maxaudron/woodox/hardware/kicad_lib/marbastlib/3d/CON_MJ-4PP-9.step

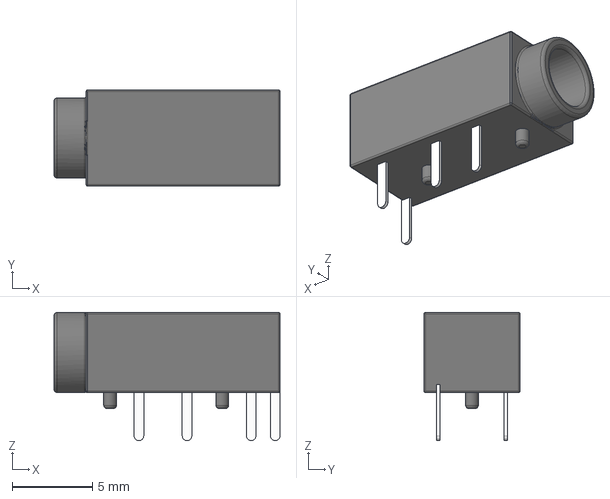
[picture p17: CAD file, 2026-05-16]
hardware/kicad_lib/marbastlib/3d/CON_MJ-4PP-9.step
14.1 x 6.00 x 8.00 mm
