maxaudron/woodox/hardware/kicad_lib/marbastlib/3d/HS_Kailh_MX.step

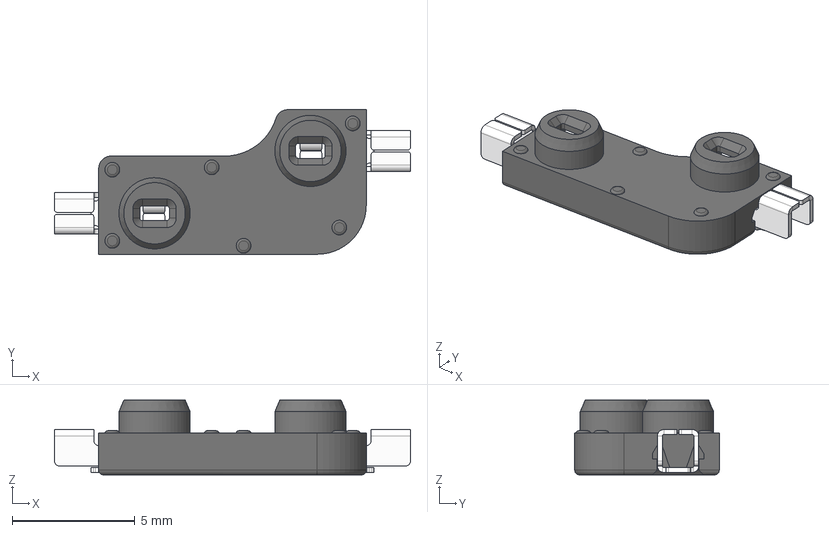
[picture p18: CAD file, 2026-05-16]
hardware/kicad_lib/marbastlib/3d/HS_Kailh_MX.step
14.5 x 5.89 x 3.05 mm
Contact x 2
