maxaudron/woodox/hardware/kicad_lib/marbastlib/3d/PNT_RKJXU1210006.step

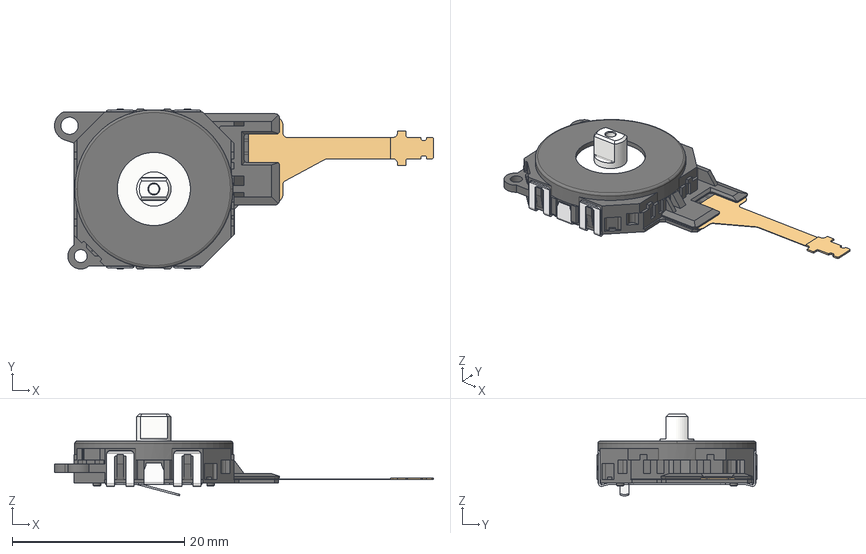
[picture p20: CAD file, 2026-05-16]
hardware/kicad_lib/marbastlib/3d/PNT_RKJXU1210006.step
44.0 x 18.6 x 9.50 mm
