maxaudron/woodox/hardware/kicad_lib/marbastlib/3d/SW_SSSS223900.step

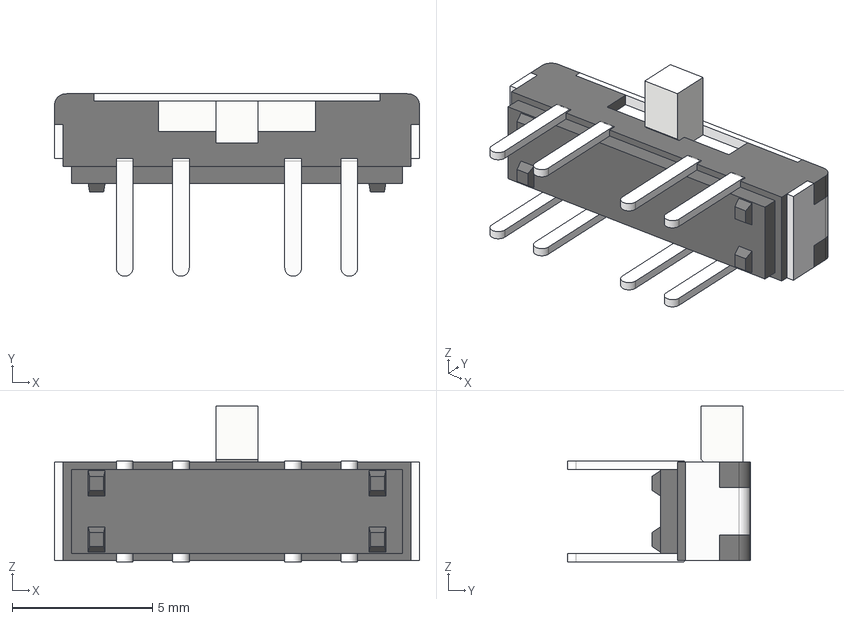
[picture p21: CAD file, 2026-05-16]
hardware/kicad_lib/marbastlib/3d/SW_SSSS223900.step
13.0 x 6.50 x 5.55 mm
