maxaudron/woodox/hardware/kicad_lib/marbastlib/3d/MSK12C02.step

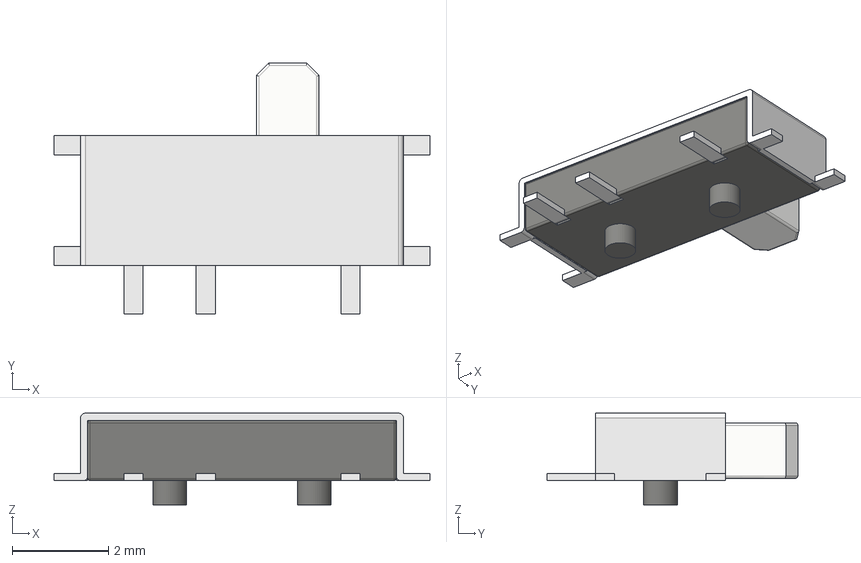
[picture p22: CAD file, 2026-05-16]
hardware/kicad_lib/marbastlib/3d/MSK12C02.step
7.80 x 5.20 x 1.90 mm
