maxaudron/woodox/hardware/kicad_lib/marbastlib/3d/ROT_EC11N.step

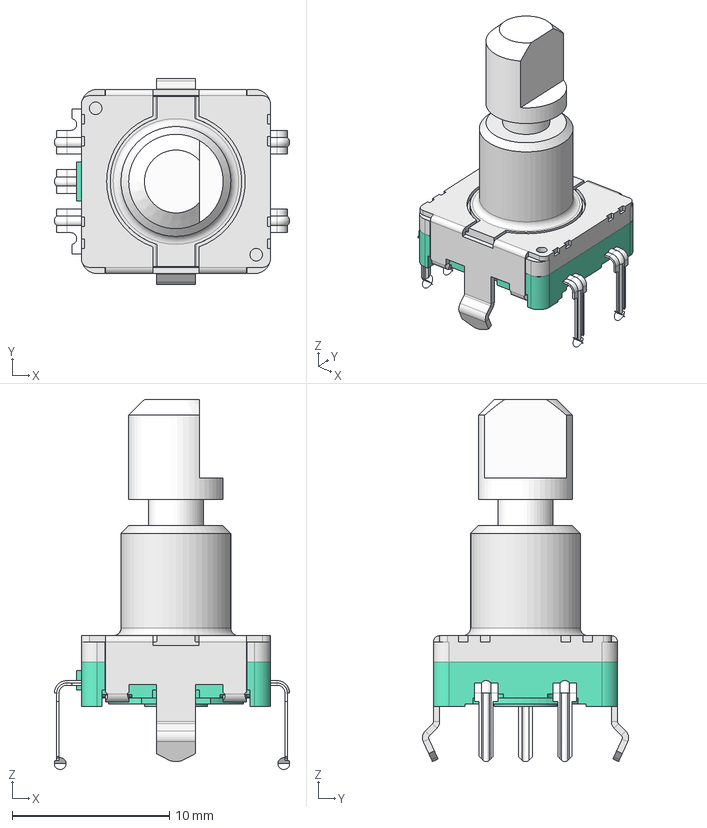
[picture p23: CAD file, 2026-05-16]
hardware/kicad_lib/marbastlib/3d/ROT_EC11N.step
14.9 x 13.1 x 23.5 mm
