maxaudron/woodox/hardware/kicad_lib/marbastlib/3d/HS_Kailh_Choc.step

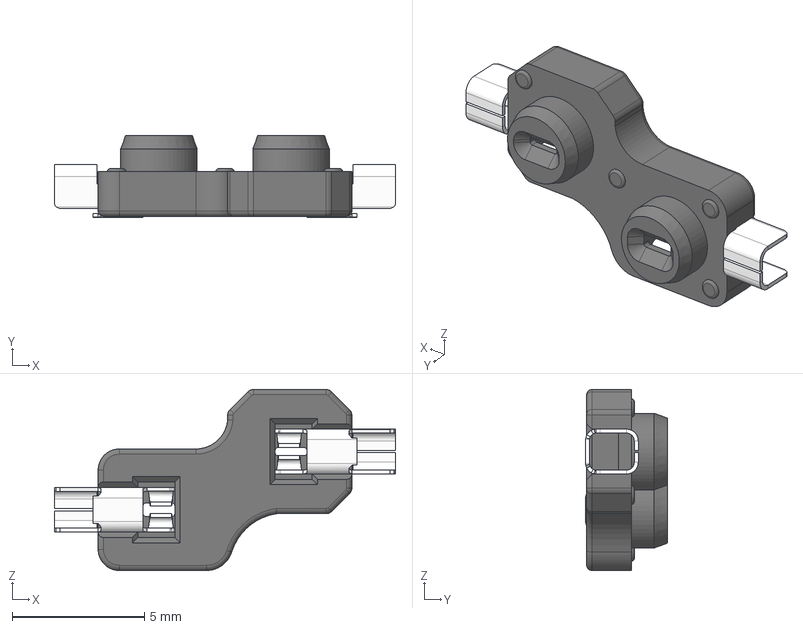
[picture p24: CAD file, 2026-05-16]
hardware/kicad_lib/marbastlib/3d/HS_Kailh_Choc.step
12.9 x 3.09 x 6.85 mm
pin x 2
socket
