maxaudron/woodox/hardware/kicad_lib/marbastlib/3d/CON_SM07B-SRSS-TB.step

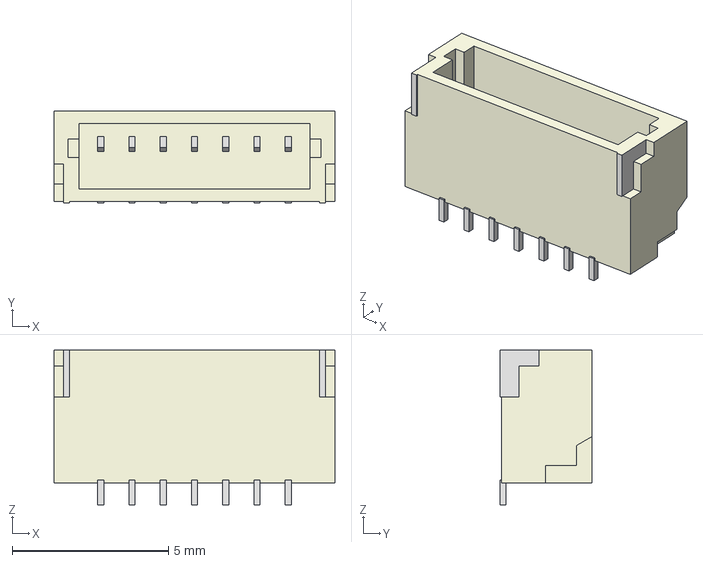
[picture p25: CAD file, 2026-05-16]
hardware/kicad_lib/marbastlib/3d/CON_SM07B-SRSS-TB.step
9.00 x 2.96 x 4.95 mm
