maxaudron/woodox/hardware/kicad_lib/marbastlib/3d/ROT_EC11E.step

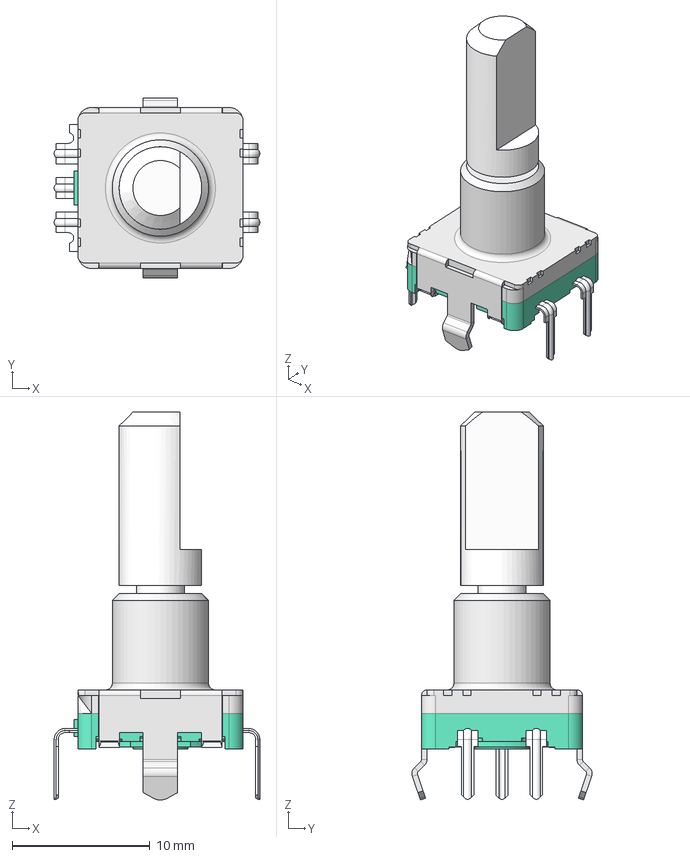
[picture p26: CAD file, 2026-05-16]
hardware/kicad_lib/marbastlib/3d/ROT_EC11E.step
14.9 x 13.1 x 28.2 mm
