maxaudron/woodox/hardware/kicad_lib/marbastlib/3d/SW_SKHLLC.step

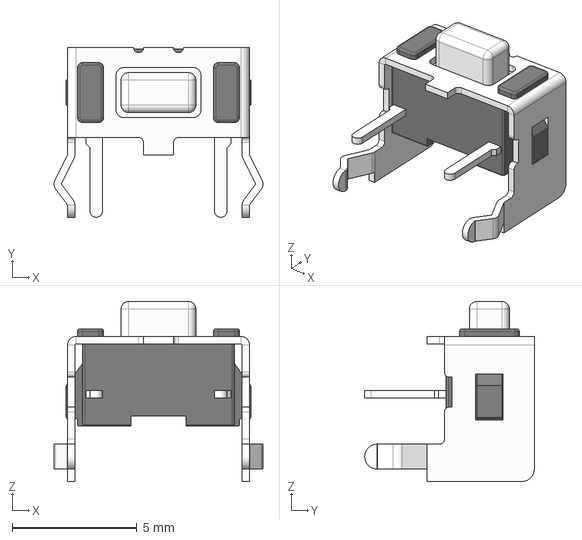
[picture p27: CAD file, 2026-05-16]
hardware/kicad_lib/marbastlib/3d/SW_SKHLLC.step
8.38 x 6.80 x 7.22 mm
