maxaudron/woodox/hardware/kicad_lib/marbastlib/3d/Crystal_FA-128.step

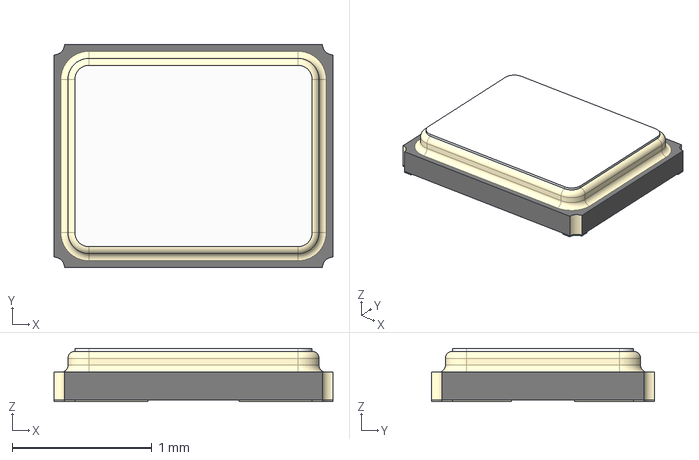
[picture p28: CAD file, 2026-05-16]
hardware/kicad_lib/marbastlib/3d/Crystal_FA-128.step
2.00 x 1.60 x 0.38 mm
