maxaudron/woodox/hardware/kicad_lib/marbastlib/3d/LED_SK6812MINI-E.step

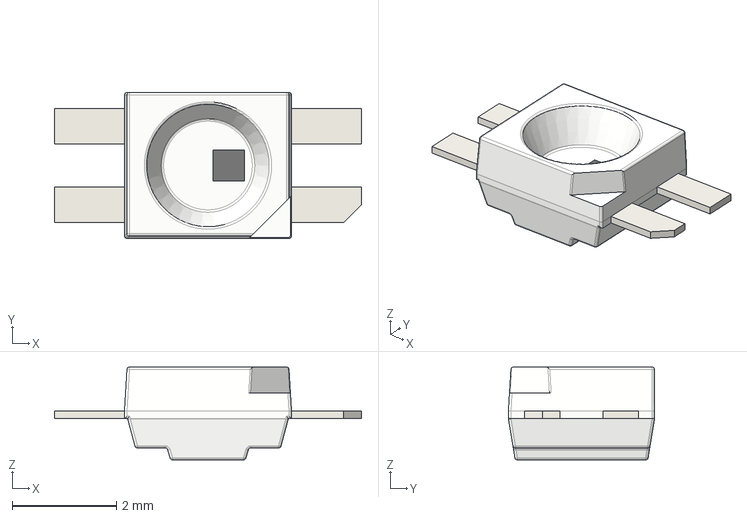
[picture p29: CAD file, 2026-05-16]
hardware/kicad_lib/marbastlib/3d/LED_SK6812MINI-E.step
5.88 x 2.80 x 1.78 mm
