maxaudron/woodox/hardware/kicad_lib/marbastlib/3d/holyiot_18010_nRF52840.step

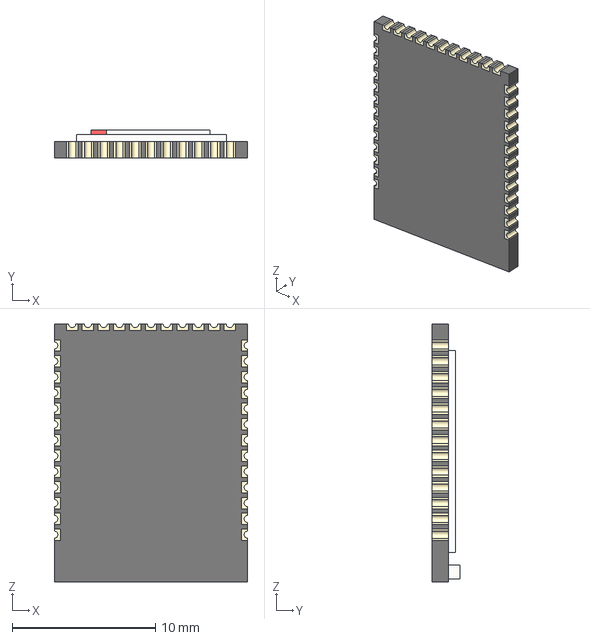
[picture p30: CAD file, 2026-05-16]
hardware/kicad_lib/marbastlib/3d/holyiot_18010_nRF52840.step
13.5 x 1.92 x 18.0 mm
