maxaudron/woodox/hardware/kicad_lib/marbastlib/3d/CON_BM02B-ACHSS.step

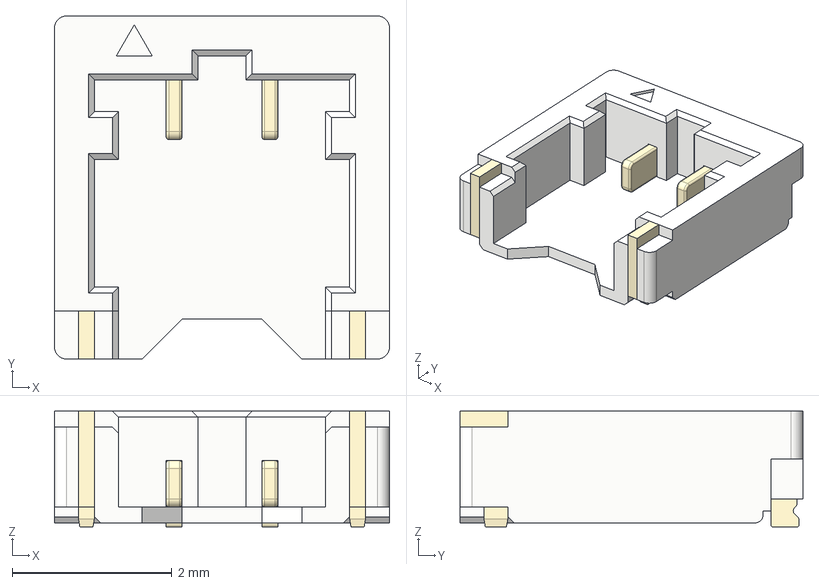
[picture p31: CAD file, 2026-05-16]
hardware/kicad_lib/marbastlib/3d/CON_BM02B-ACHSS.step
4.20 x 4.30 x 1.45 mm
