maxaudron/woodox/hardware/kicad_lib/marbastlib/3d/moko_mk08a_nRF52840.step

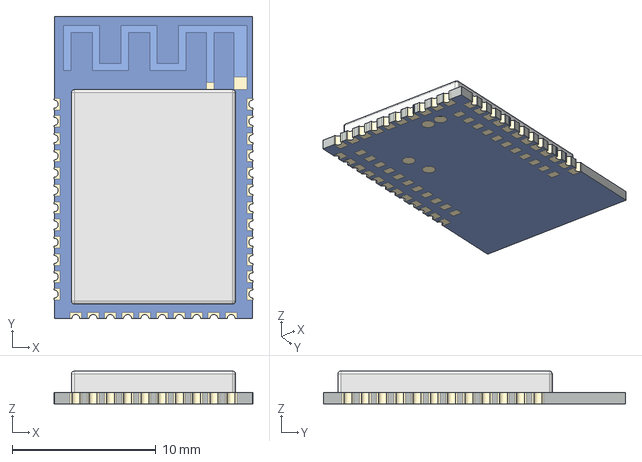
[picture p32: CAD file, 2026-05-16]
hardware/kicad_lib/marbastlib/3d/moko_mk08a_nRF52840.step
13.8 x 21.0 x 2.29 mm
