maxaudron/woodox/hardware/kicad_lib/marbastlib/3d/CON_SM08B-SRSS-TB.step

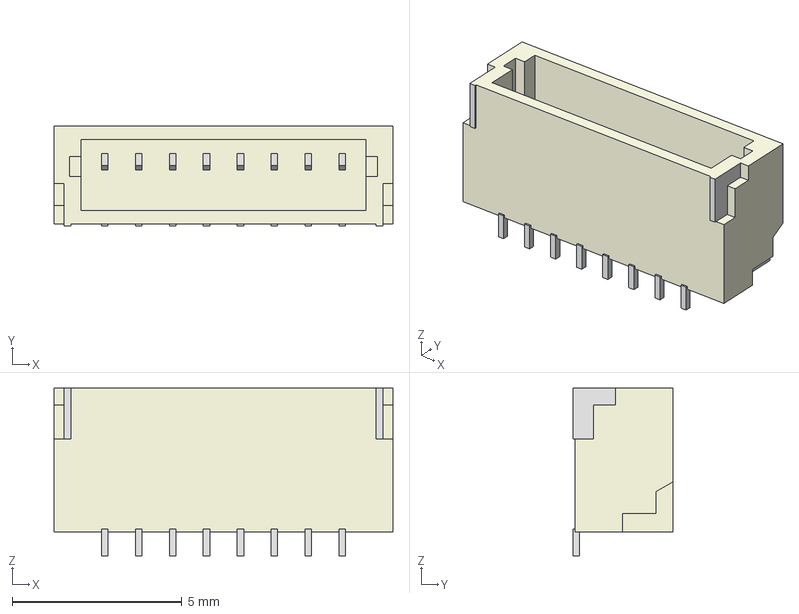
[picture p33: CAD file, 2026-05-16]
hardware/kicad_lib/marbastlib/3d/CON_SM08B-SRSS-TB.step
10.0 x 2.96 x 4.95 mm
