maxaudron/woodox/hardware/kicad_lib/marbastlib/3d/SW_ESP3020.step

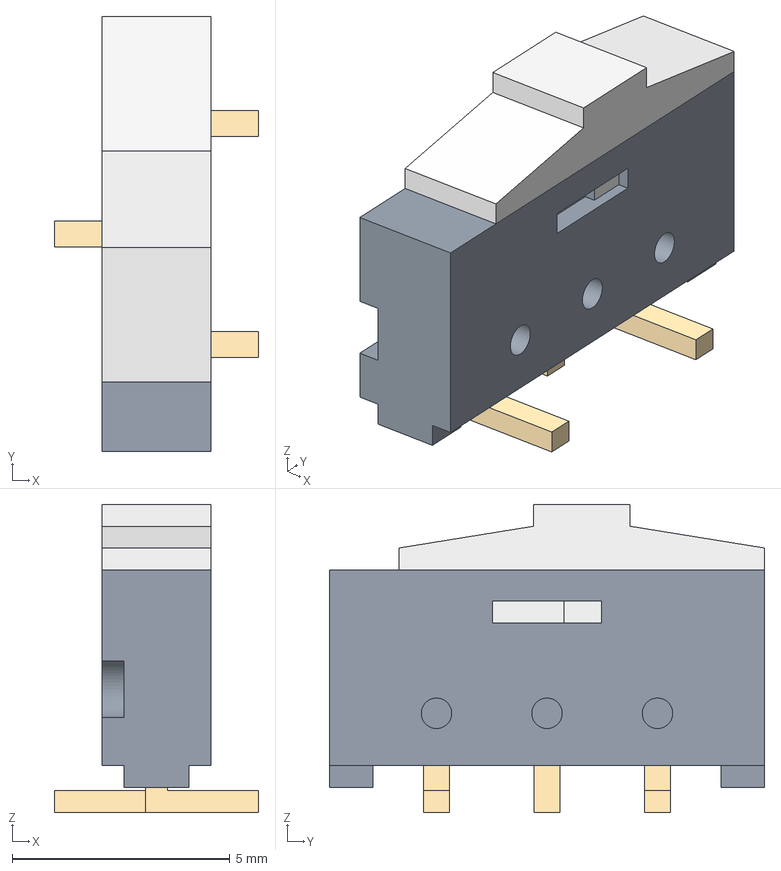
[picture p34: CAD file, 2026-05-16]
hardware/kicad_lib/marbastlib/3d/SW_ESP3020.step
4.70 x 10.0 x 7.08 mm
