maxaudron/woodox/hardware/kicad_lib/marbastlib/3d/CON_SM02B-SRSS-TB.step

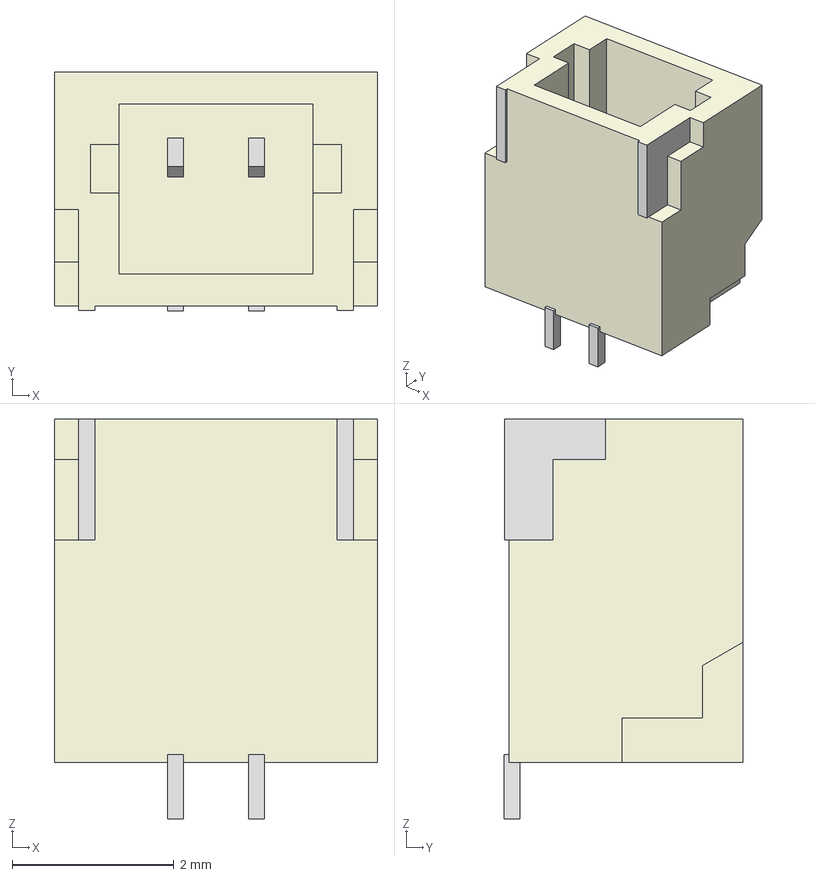
[picture p36: CAD file, 2026-05-16]
hardware/kicad_lib/marbastlib/3d/CON_SM02B-SRSS-TB.step
4.00 x 2.96 x 4.95 mm
