maxaudron/woodox/boards/rp2040/src/usb.rs

use cortex_m::prelude::*;

use defmt::{debug, info};

use usb_device::class_prelude::*;
use usb_device::prelude::*;
use usbd_human_interface_device::device::DeviceClass;
use usbd_human_interface_device::device::keyboard::NKROBootKeyboardConfig;
use usbd_human_interface_device::prelude::*;

use fugit::ExtU32;

use crate::hal::Timer;
use woodox_lib::matrix;

pub fn usb<U>(timer: Timer, usb_bus: UsbBusAllocator<U>) -> !
where
    U: UsbBus + Sized,
{
    let mut keyboard = UsbHidClassBuilder::new()
        .add_device(NKROBootKeyboardConfig::default())
        .build(&usb_bus);

    //https://pid.codes
    let mut usb_dev = UsbDeviceBuilder::new(&usb_bus, UsbVidPid(0x1209, 0x0001))
        .strings(&[StringDescriptors::default()
            .manufacturer("usbd-human-interface-device")
            .product("NKRO Keyboard")
            .serial_number("TEST")])
        .unwrap()
        .build();

    let mut tick_count_down = timer.count_down();
    tick_count_down.start(1.millis());

    info!("starting usb loop");
    loop {
        if tick_count_down.wait().is_ok() {
            let keys = matrix::Keymap::keyboard();

            match keyboard.device().write_report(keys) {
                Err(UsbHidError::WouldBlock) => {}
                Err(UsbHidError::Duplicate) => {}
                Ok(_) => {}
                Err(e) => {
                    core::panic!("Failed to write keyboard report: {:?}", e)
                }
            };

            match keyboard.device().tick() {
                Err(UsbHidError::WouldBlock) => {}
                Ok(_) => {}
                Err(e) => {
                    core::panic!("Failed to process keyboard tick: {:?}", e)
                }
            };

            matrix::Keymap::clear_oneshot();
        }

        if usb_dev.poll(&mut [&mut keyboard]) {
            match keyboard.device().read_report() {
                Err(UsbError::WouldBlock) => {
                    //do nothing
                }
                Err(e) => {
                    core::panic!("Failed to read keyboard report: {:?}", e)
                }
                Ok(leds) => {
                    debug!(
                        "got leds: {} {} {} {} {}",
                        leds.num_lock, leds.caps_lock, leds.scroll_lock, leds.compose, leds.kana
                    )
                }
            }
        }
    }
}
